OLIMEX/ESP32-ADF/HARDWARE/ESP32-ADF Rev.C/3d/ESP32-WROVER-I-56544.STEP

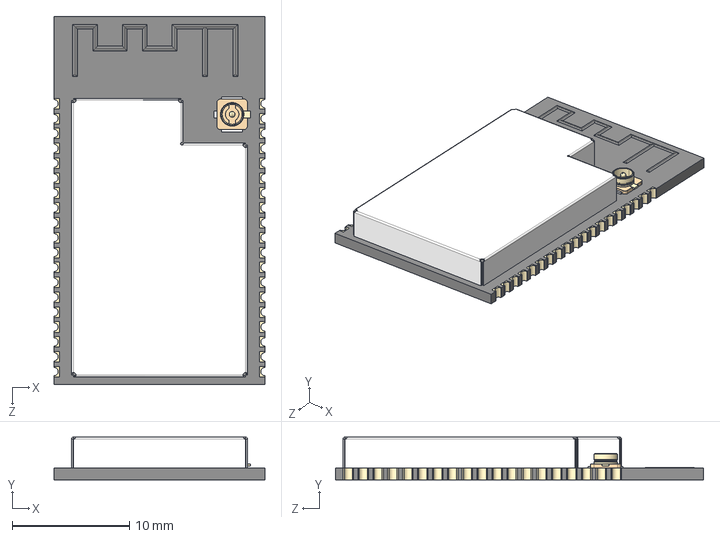
[picture p15: CAD file, 2020-11-23]
HARDWARE/ESP32-ADF Rev.C/3d/ESP32-WROVER-I-56544.STEP
18.0 x 3.65 x 31.4 mm
