OLIMEX/ESP32-ADF/HARDWARE/ESP32-ADF Rev.C/3d/T1107A.STEP

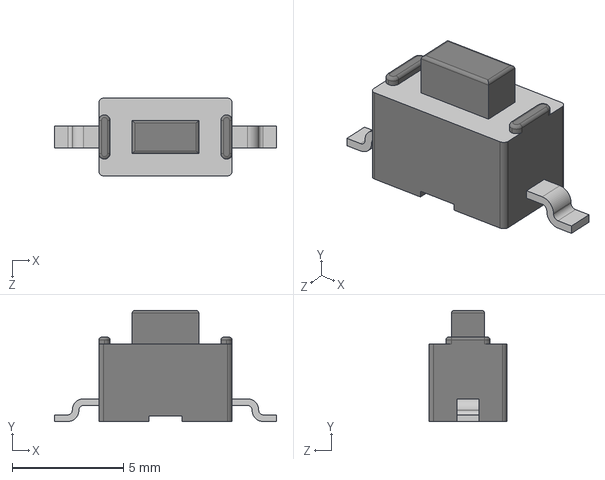
[picture p16: CAD file, 2020-11-23]
HARDWARE/ESP32-ADF Rev.C/3d/T1107A.STEP
10.0 x 5.00 x 3.50 mm
