OLIMEX/ESP32-ADF/HARDWARE/ESP32-ADF Rev.C/3d/QSG5032.step

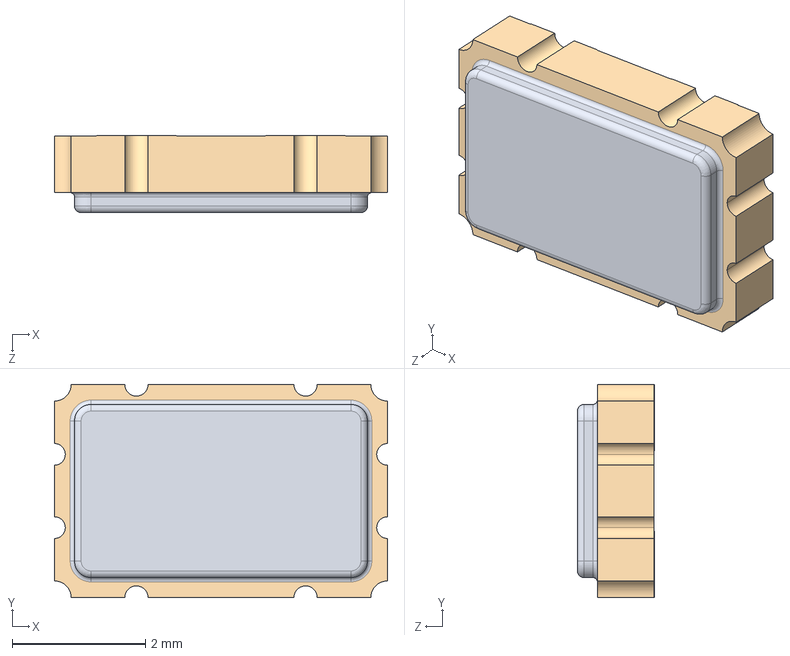
[picture p17: CAD file, 2020-11-23]
HARDWARE/ESP32-ADF Rev.C/3d/QSG5032.step
5.00 x 3.20 x 1.16 mm
