OLIMEX/ESP32-ADF/HARDWARE/ESP32-ADF Rev.C/3d/rubber_feet.step

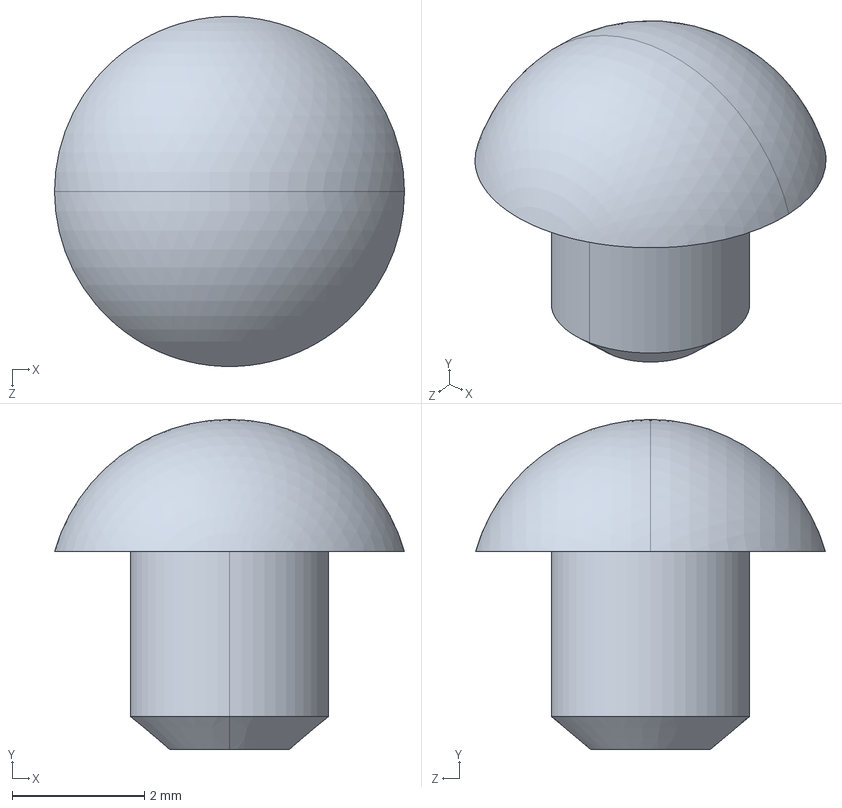
[picture p18: CAD file, 2020-11-23]
HARDWARE/ESP32-ADF Rev.C/3d/rubber_feet.step
5.30 x 5.00 x 5.30 mm
