OLIMEX/ESP32-ADF/HARDWARE/ESP32-ADF Rev.C/3d/User_Library-Parallax-IR.step

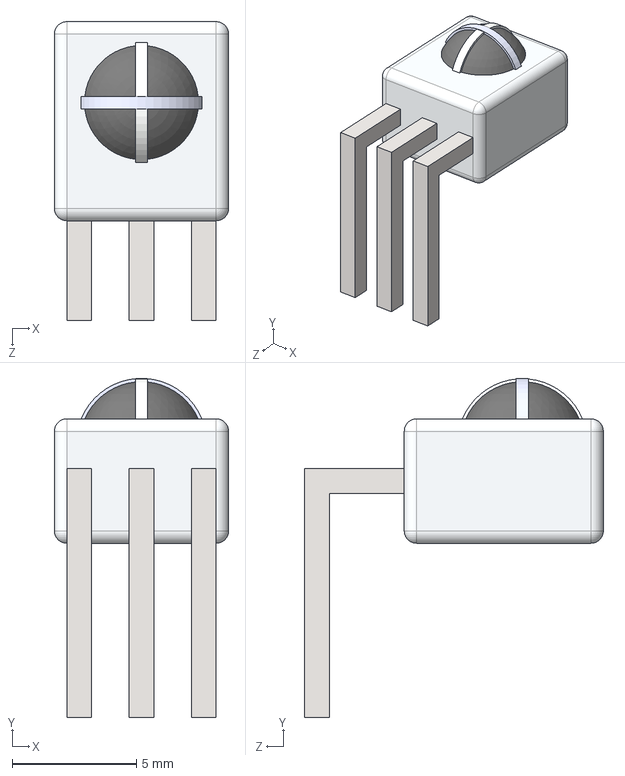
[picture p19: CAD file, 2020-11-23]
HARDWARE/ESP32-ADF Rev.C/3d/User_Library-Parallax-IR.step
7.00 x 13.6 x 12.0 mm
