OLIMEX/ESP32-ADF/HARDWARE/ESP32-ADF Rev.C/3d/cma-6542pf.stp

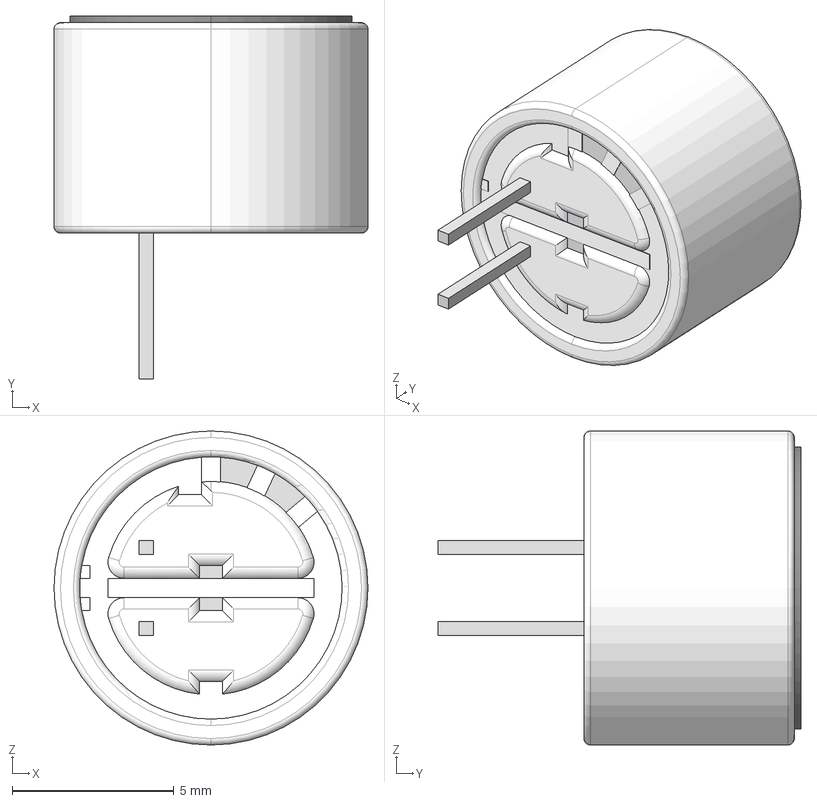
[picture p20: CAD file, 2020-11-23]
HARDWARE/ESP32-ADF Rev.C/3d/cma-6542pf.stp
9.70 x 11.2 x 9.70 mm
