OLIMEX/ESP32-ADF/SOFTWARE/esp-va-sdk/board_support_pkgs/olimex_esp32_adf/audio_board/audio_board_olimex/audio_board_olimex/led_olimex.h

// Copyright 2018 Espressif Systems (Shanghai) PTE LTD
// All rights reserved.

#ifndef _LED_OLIMEX_H_
#define _LED_OLIMEX_H_

#include <stdint.h>
#include <stdlib.h>
#include <stdbool.h>
#include "va_led.h"

void led_lyrat_pattern_init(va_led_config_t **va_led_lyrat_pat);

#endif /* _LED_OLIMEX_H_ */
